DavidRodrii/LoRaware-Project/imgs/LW-Assem-BotUp.png

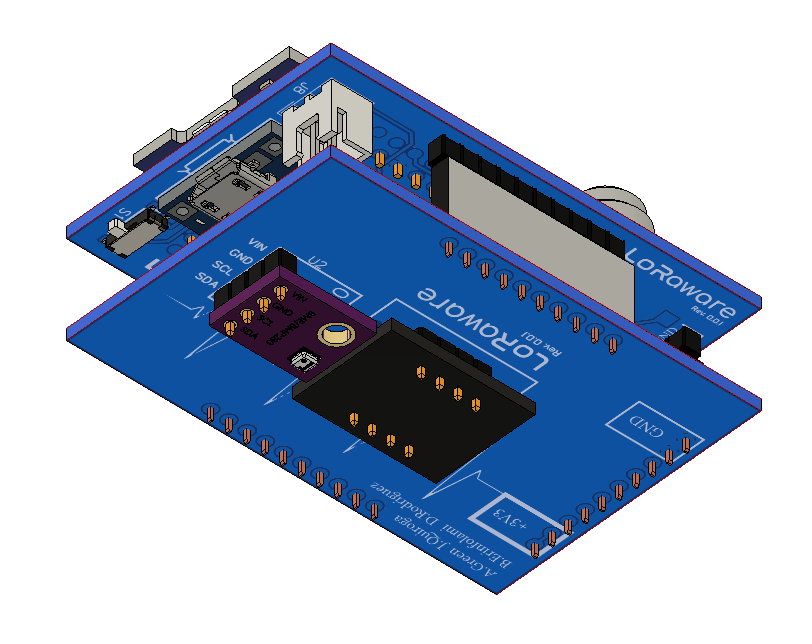
imgs/LW-Assem-BotUp.png
