DavidRodrii/LoRaware-Project/imgs/LW-Enclosure-ISO.png

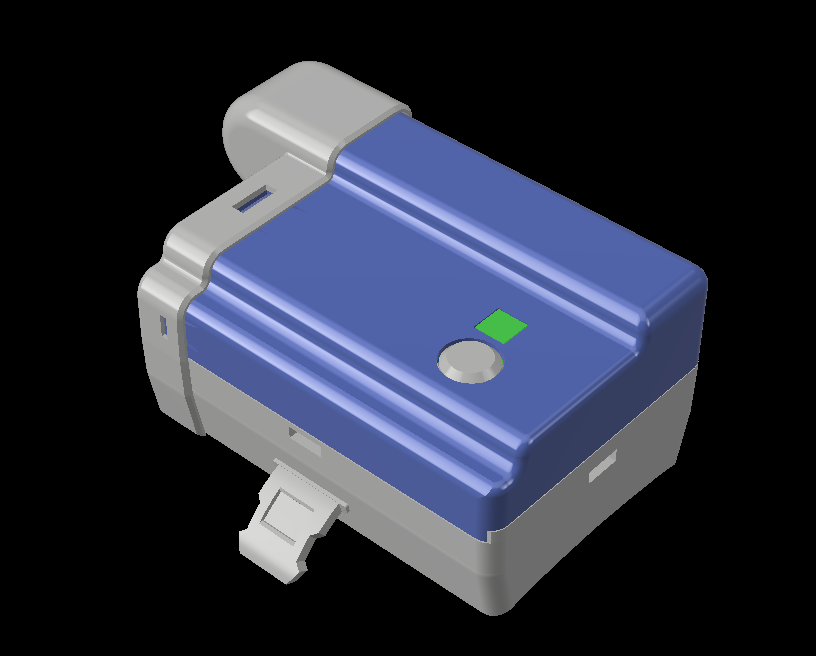
imgs/LW-Enclosure-ISO.png
