DavidRodrii/LoRaware-Project/imgs/LW-PCB-assem-BotUp.png

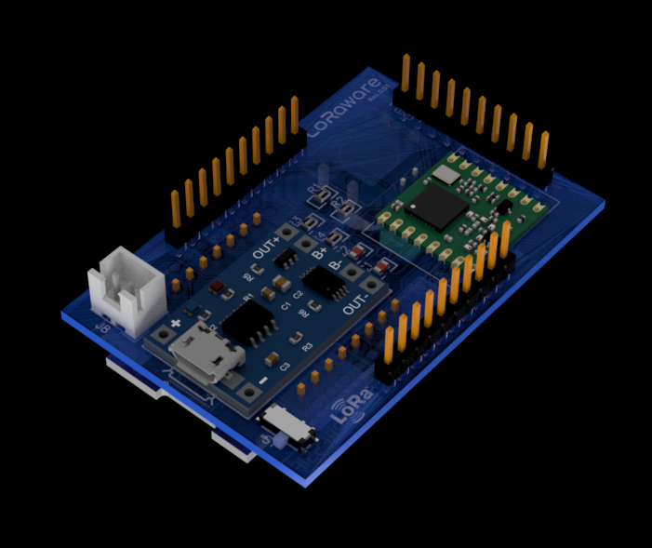
imgs/LW-PCB-assem-BotUp.png
