DavidRodrii/LoRaware-Project/imgs/lware-cutaway1.png

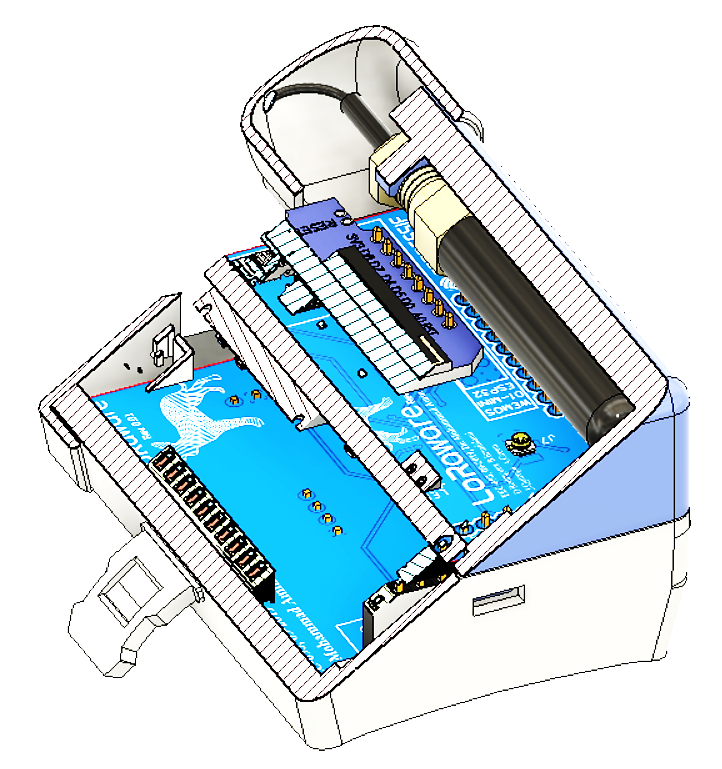
imgs/lware-cutaway1.png
