DavidRodrii/LoRaware-Project/imgs/Testing&Assembly/BandConcept.jpg

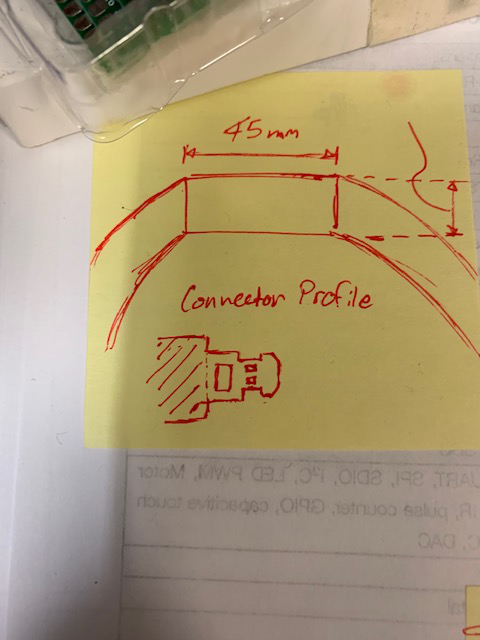
imgs/Testing&Assembly/BandConcept.jpg
