DavidRodrii/LoRaware-Project/PCB/PCB imgs/BottomPCB-BottomSide-Final.PNG

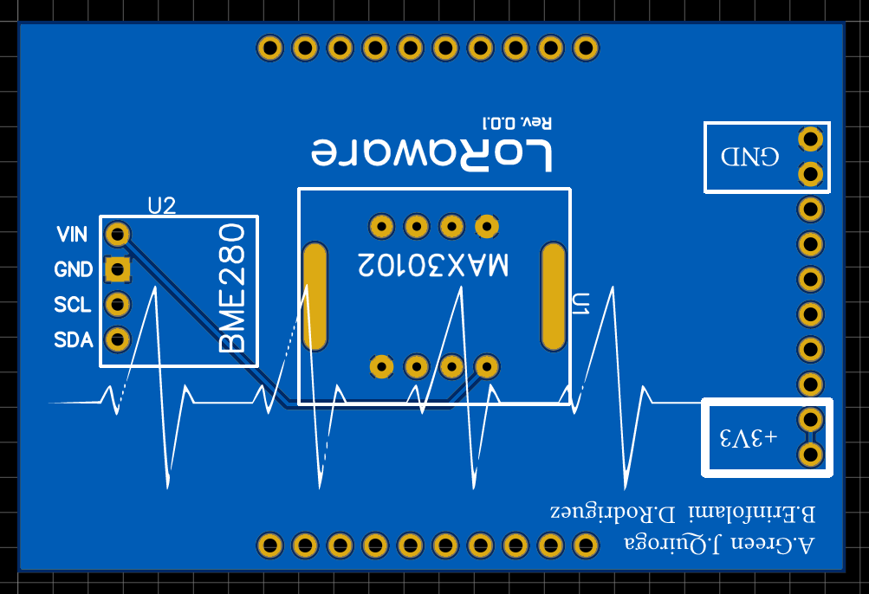
PCB/PCB imgs/BottomPCB-BottomSide-Final.PNG
