DavidRodrii/LoRaware-Project/PCB/PCB imgs/BottomPCB-TopSide-Final.PNG

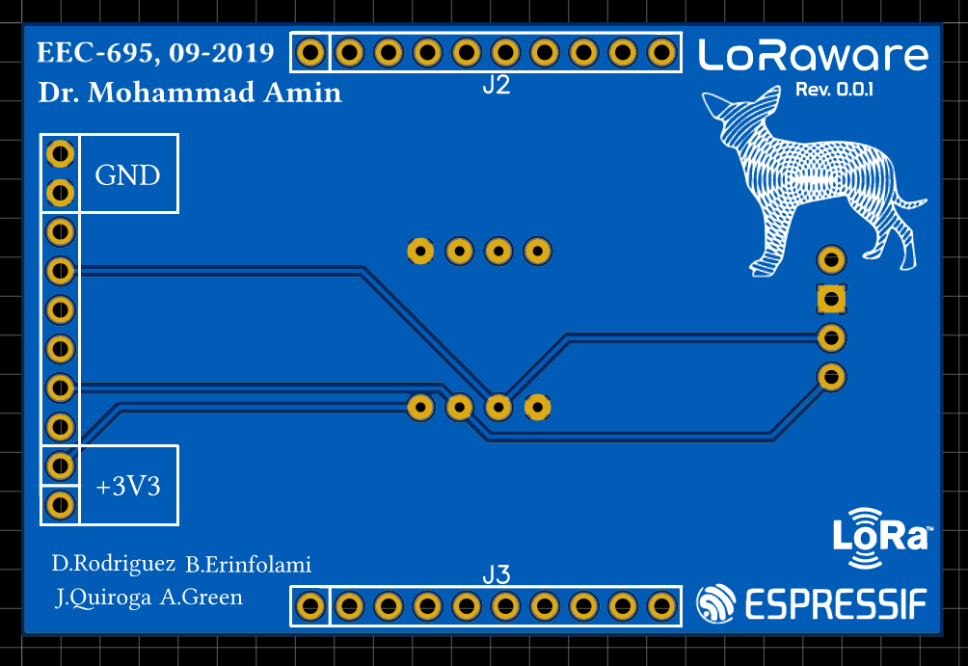
PCB/PCB imgs/BottomPCB-TopSide-Final.PNG
