DavidRodrii/LoRaware-Project/PCB/PCB imgs/TopPCB-BottomSide-Final.PNG

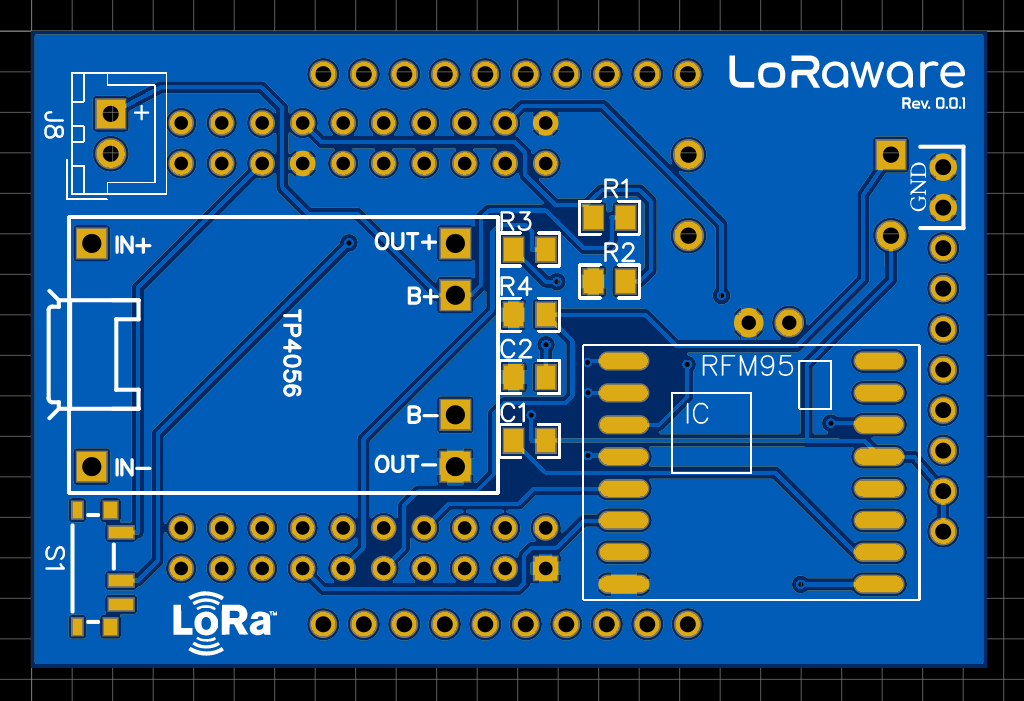
PCB/PCB imgs/TopPCB-BottomSide-Final.PNG
