DavidRodrii/LoRaware-Project/PCB/PCB imgs/TopPCB-TopSide-Final.PNG

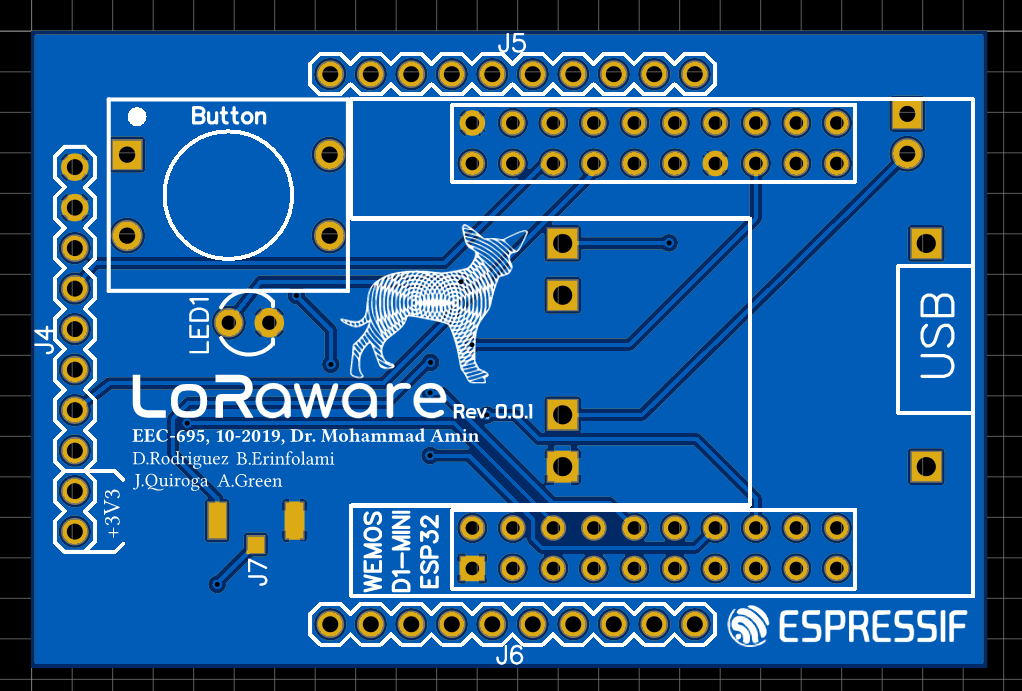
PCB/PCB imgs/TopPCB-TopSide-Final.PNG
