DavidRodrii/LoRaware-Project/Raspi/Grafana/GrafanaDash.PNG

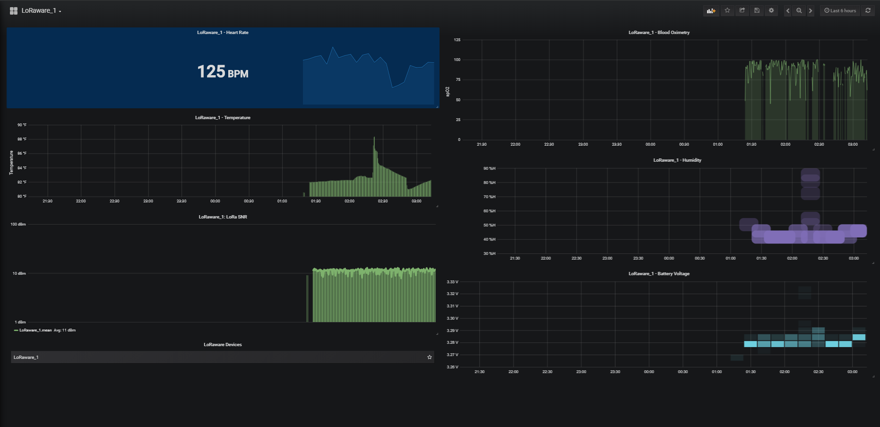
Raspi/Grafana/GrafanaDash.PNG
