DavidRodrii/LoRaware-Project/Raspi/Grafana/LoRa_SNR.png

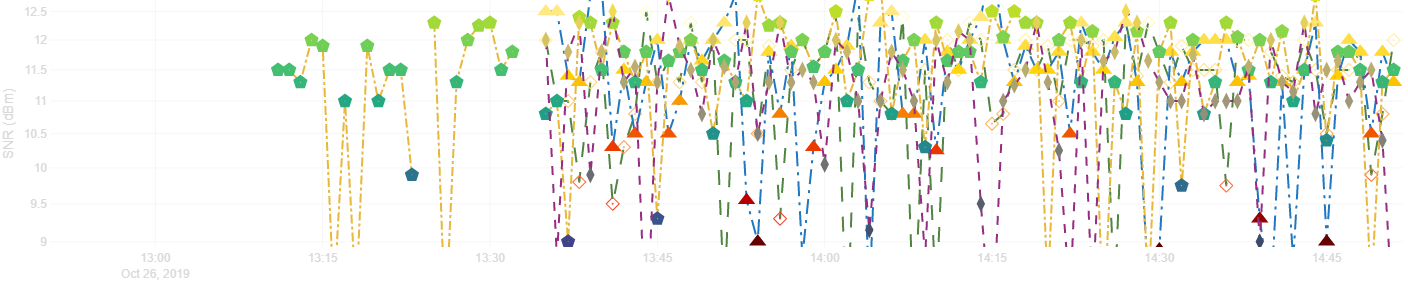
Raspi/Grafana/LoRa_SNR.png
