DavidRodrii/LoRaware-Project/Raspi/NodeRed/MainFlow.PNG

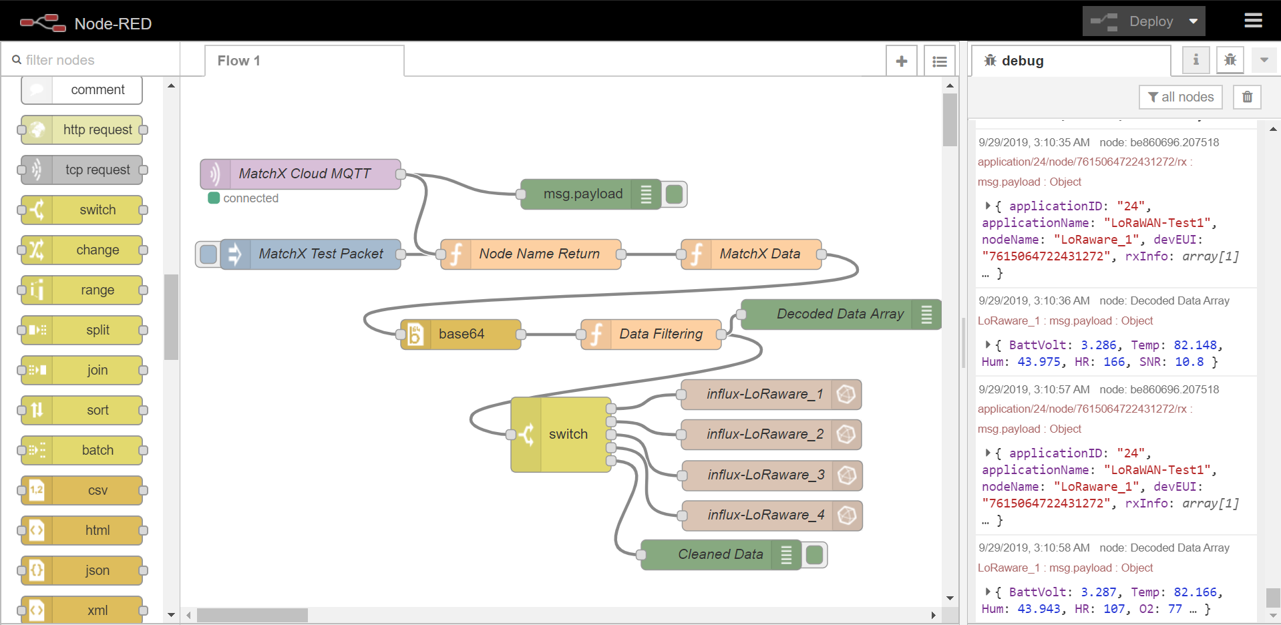
Raspi/NodeRed/MainFlow.PNG
