DavidRodrii/LoRaware-Project/imgs/Testing&Assembly/microSolder.jpg

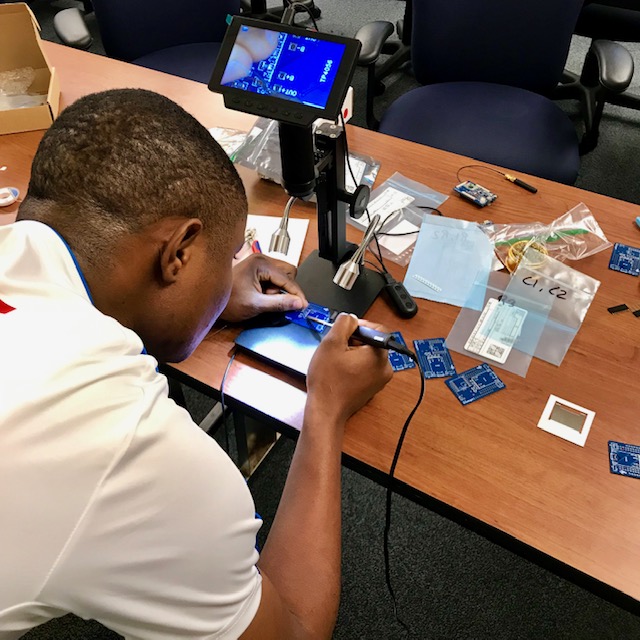
imgs/Testing&Assembly/microSolder.jpg
