DavidRodrii/LoRaware-Project/imgs/Testing&Assembly/Myst.jpg

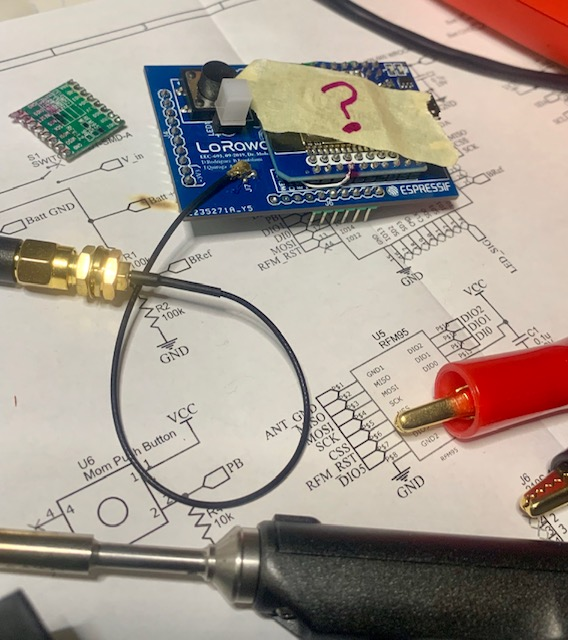
imgs/Testing&Assembly/Myst.jpg
