DavidRodrii/LoRaware-Project/imgs/Testing&Assembly/Testing1-1.jpg

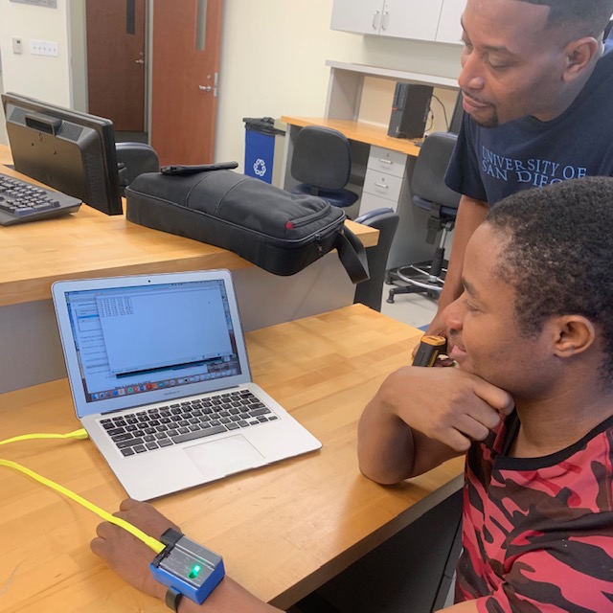
imgs/Testing&Assembly/Testing1-1.jpg
