DavidRodrii/LoRaware-Project/imgs/Testing&Assembly/Testing1-2.jpg

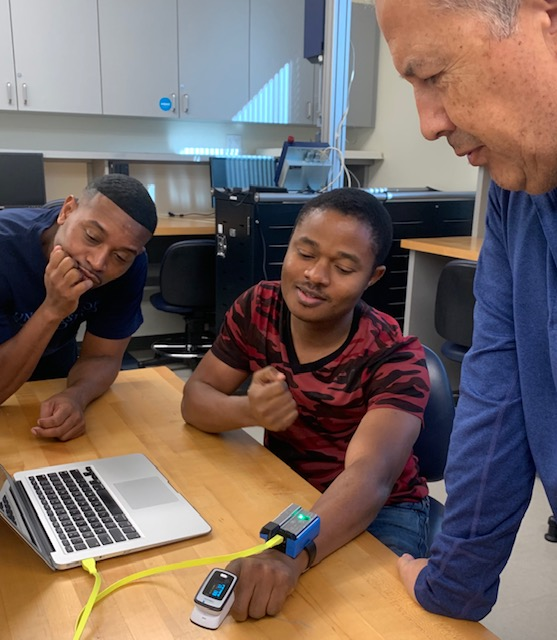
imgs/Testing&Assembly/Testing1-2.jpg
