DavidRodrii/LoRaware-Project/imgs/Testing&Assembly/Testing3-1.jpg

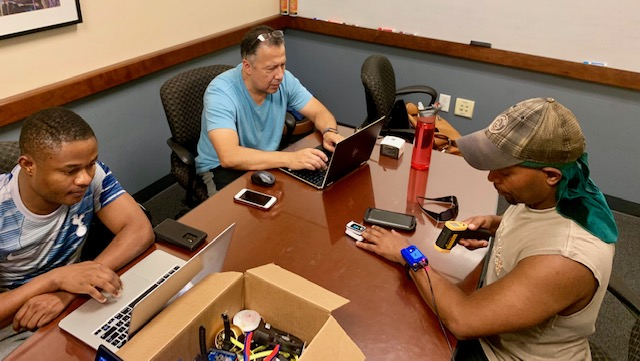
imgs/Testing&Assembly/Testing3-1.jpg
