DavidRodrii/LoRaware-Project/imgs/Testing&Assembly/Testing3-2.jpg

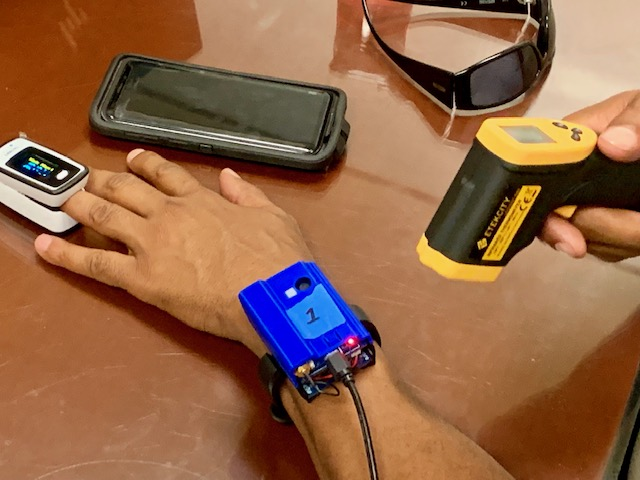
imgs/Testing&Assembly/Testing3-2.jpg
